dabecart/OCXOController/sw/OCXOController_v2/src/USB/USBComms.h

#ifndef USB_COMMS_h
#define USB_COMMS_h

#include "stm32g473xx.h"
#include "stm32g4xx_hal.h"
#include "usb_device.h"
#include "usbd_cdc_if.h"

#include "buffers/CircularBuffer.h"

#define USB_TIMEOUT_ms 200

void initUSBComms();

uint8_t sendMessageUSB(uint8_t* message, uint32_t messageLength);

uint8_t readMessageUSB(uint32_t maxLength, uint8_t* message, uint32_t* messageLength);

void setUSBConnected(uint8_t connected);

#endif // USB_COMMS_h
