dabecart/OCXOController/sw/OCXOController_v2/src/GUI.h

#ifndef GUI_h
#define GUI_h

#include "math.h"
#include "stdlib.h"

#include "Defines.h"
#include "TFT/ST7735.h"
#include "GUI/Screen.h"
#include "GUI/Overlay.h"

uint8_t initGUI(SPI_HandleTypeDef* hspi, TIM_HandleTypeDef* guitim);

void updateGUI();

void requestScreenChange(ScreenID nextScreen, void** newScreenArgs, uint8_t useTransition);

void transferScreenToTFT();
void transferToTFTEnded();

extern uint8_t updateGUIInIRQ;
extern TFT guiTFT;

#endif // GUI_h
